tebl/Amiga-Mouse-Switch/gallery/2021-03-31 23.02.21.jpg

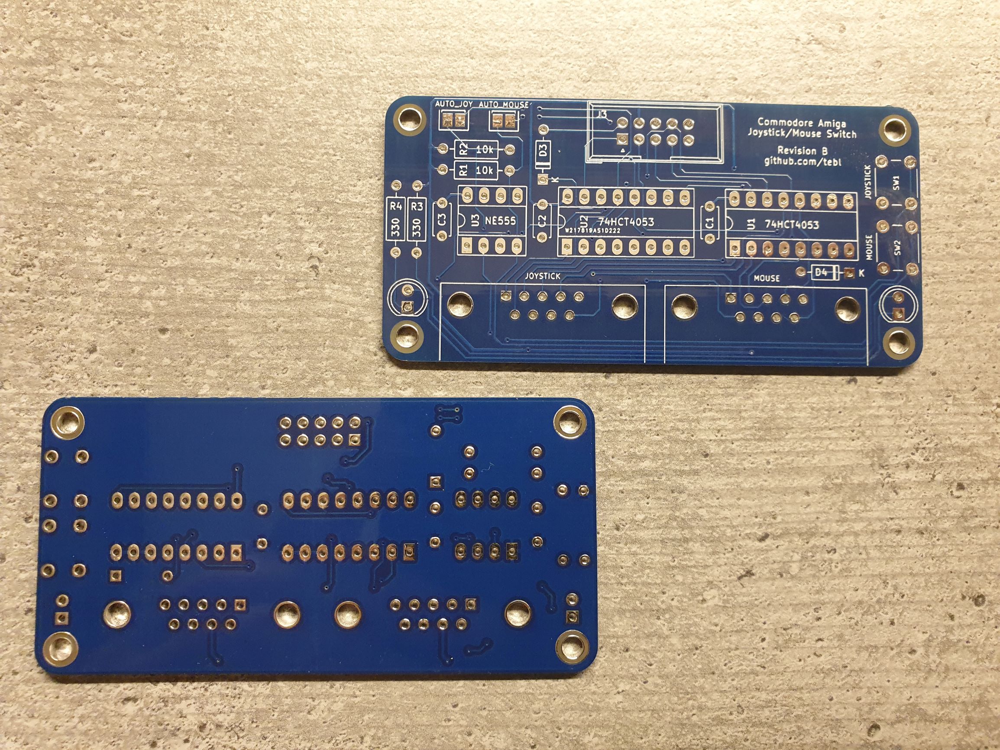
gallery/2021-03-31 23.02.21.jpg
