tebl/Amiga-Mouse-Switch/gallery/2021-03-31 23.43.13.jpg

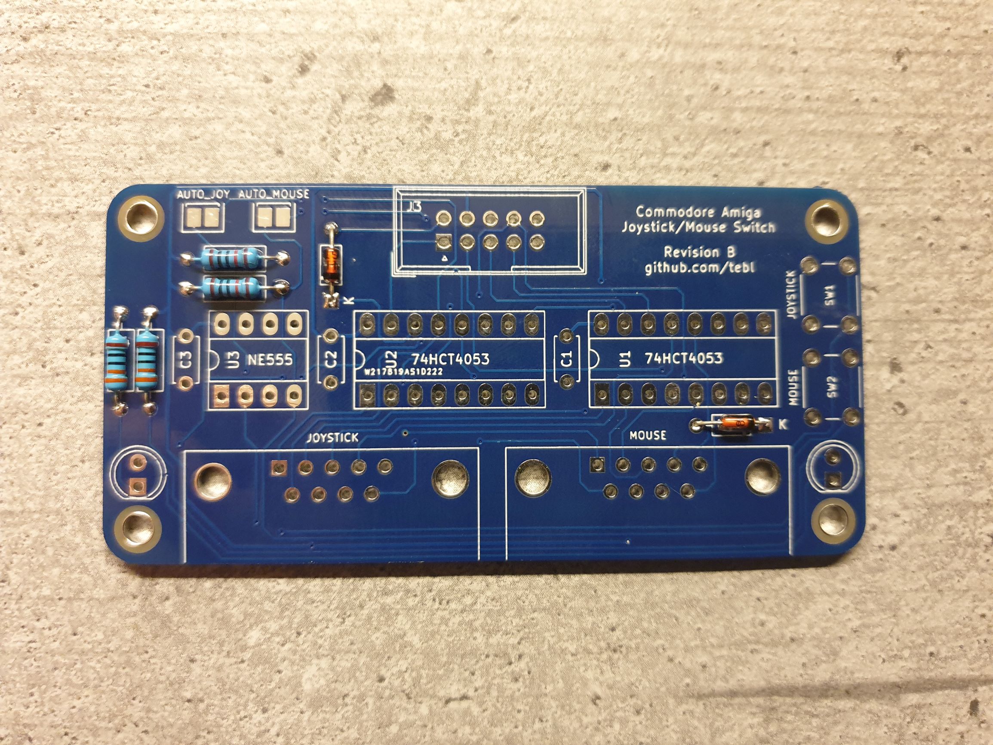
gallery/2021-03-31 23.43.13.jpg
