tebl/Amiga-Mouse-Switch/gallery/2021-04-01 00.36.23.jpg

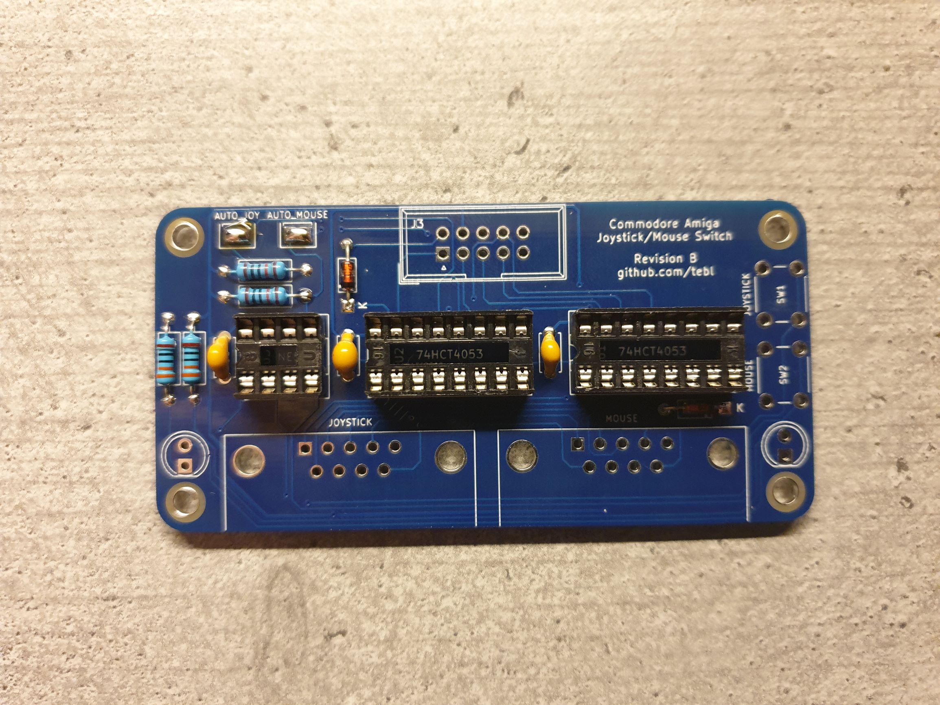
gallery/2021-04-01 00.36.23.jpg
