tebl/Amiga-Mouse-Switch/gallery/2021-04-01 01.14.33.jpg

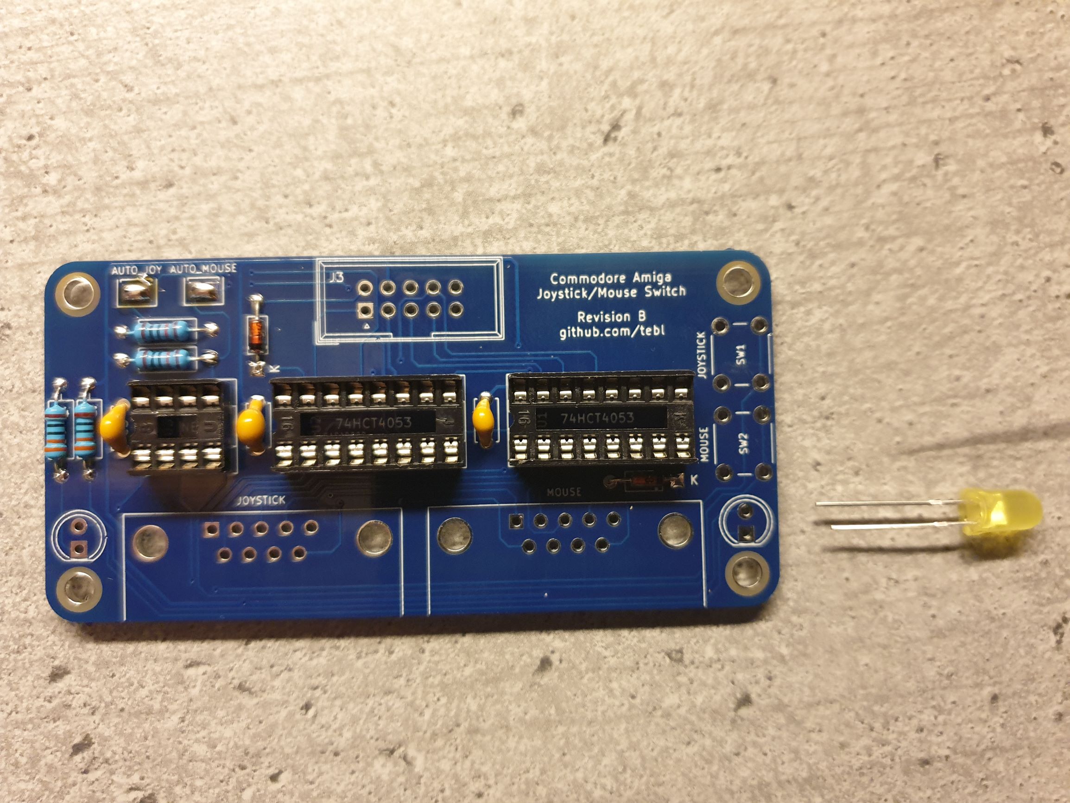
gallery/2021-04-01 01.14.33.jpg
