tebl/Amiga-Mouse-Switch/gallery/2021-04-01 01.17.28.jpg

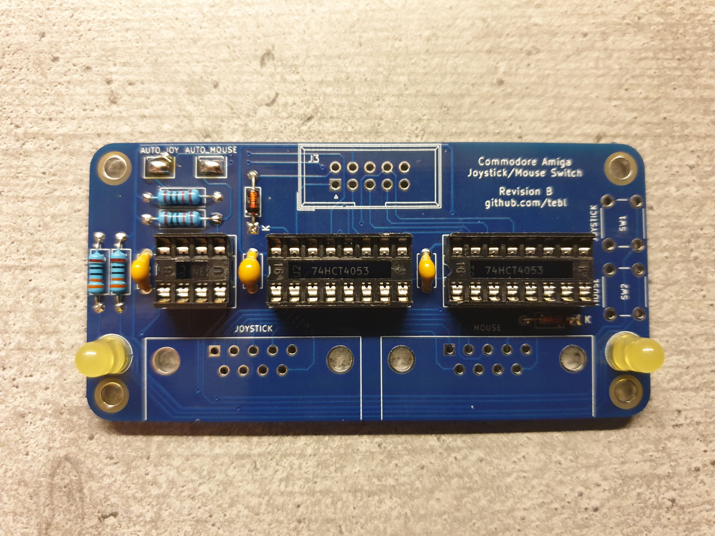
gallery/2021-04-01 01.17.28.jpg
