tebl/Amiga-Mouse-Switch/gallery/2021-04-01 01.47.34.jpg

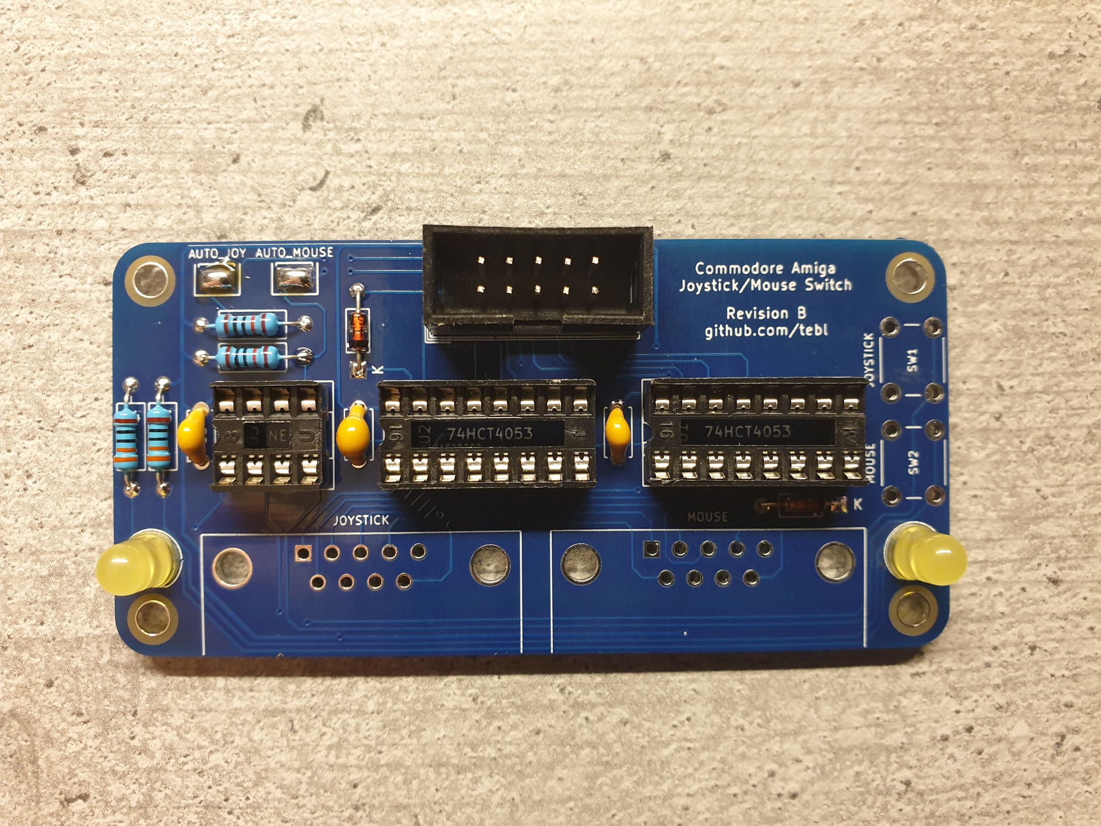
gallery/2021-04-01 01.47.34.jpg
