tebl/Amiga-Mouse-Switch/gallery/2021-04-01 01.50.25.jpg

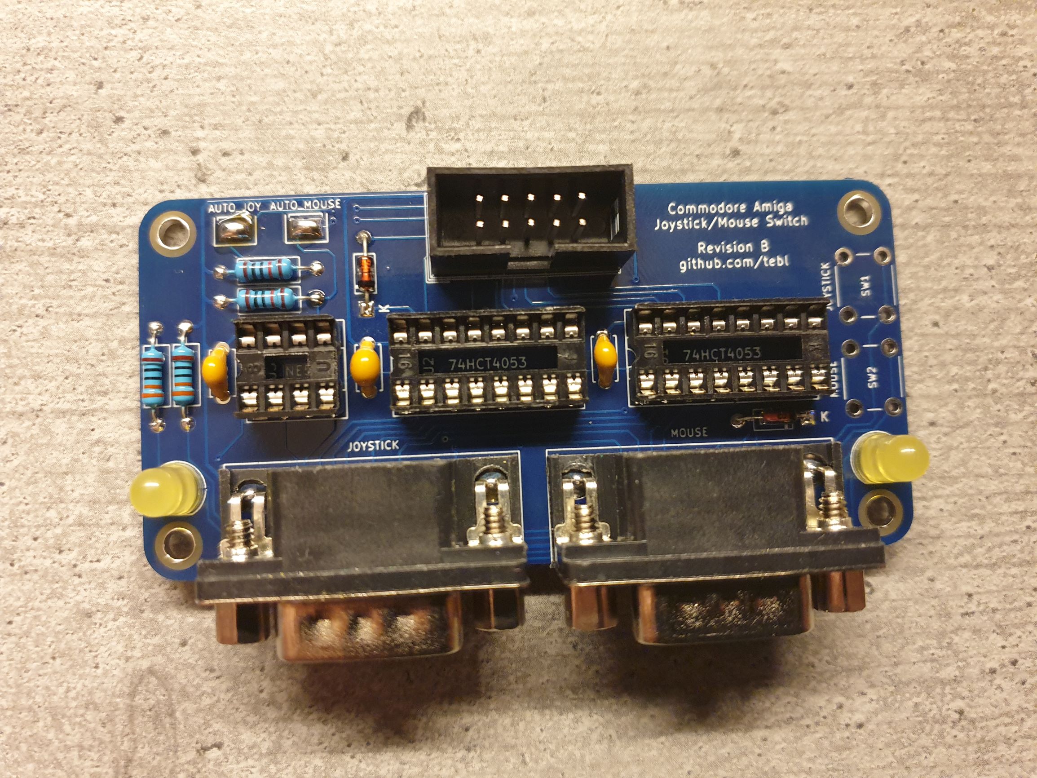
gallery/2021-04-01 01.50.25.jpg
