tebl/Amiga-Mouse-Switch/gallery/2021-04-01 02.00.01.jpg

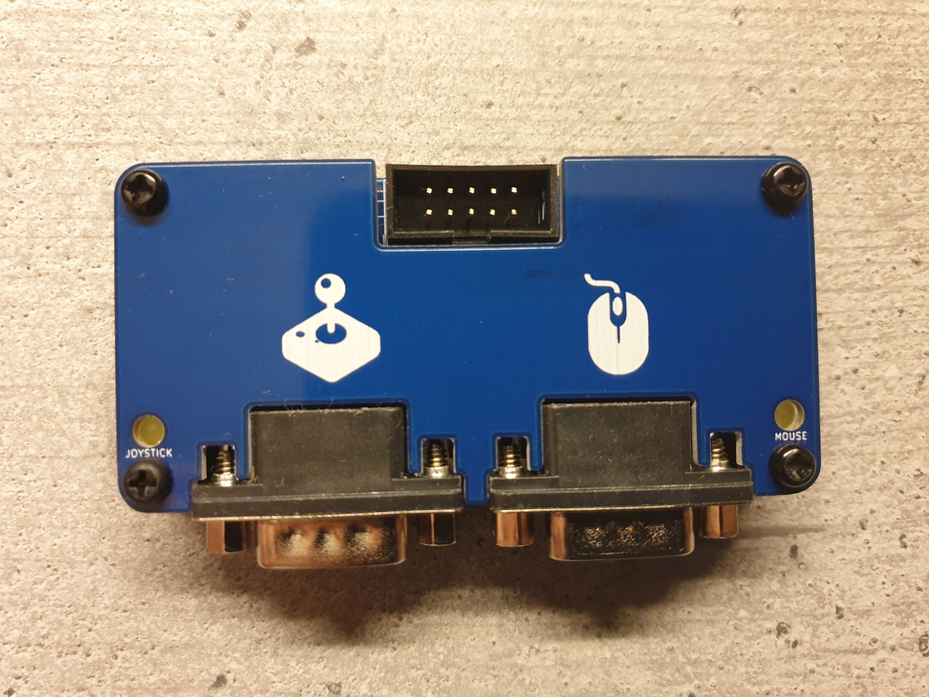
gallery/2021-04-01 02.00.01.jpg
