tebl/Amiga-Mouse-Switch/gallery/Amiga Mouse Switch Faceplate B1.png

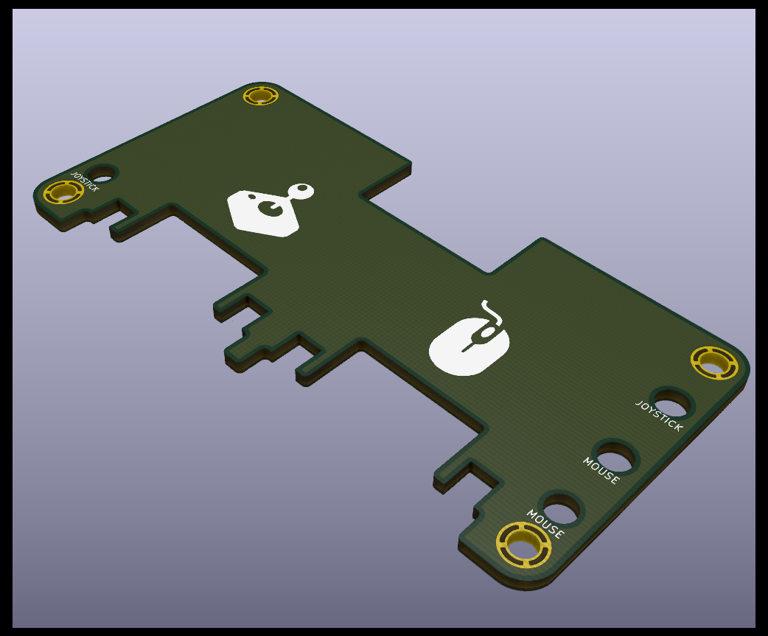
gallery/Amiga Mouse Switch Faceplate B1.png
