tebl/Amiga-Mouse-Switch/gallery/PCB_Preview.png

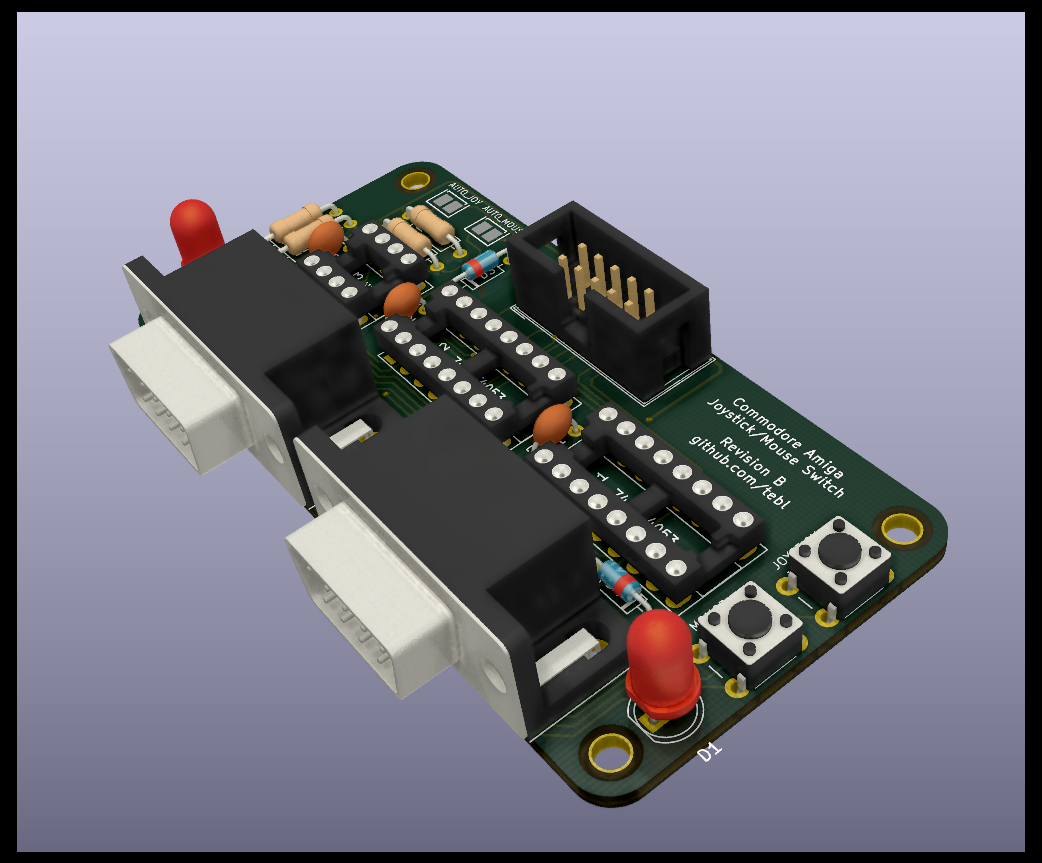
gallery/PCB_Preview.png
